tebl/C64-Kernal-Switcher/gallery/12f629 #1.PNG

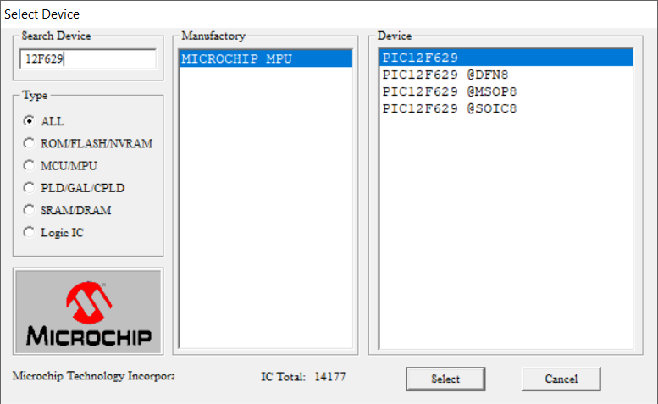
gallery/12f629 #1.PNG
