tebl/C64-Kernal-Switcher/gallery/12f629 #3.PNG

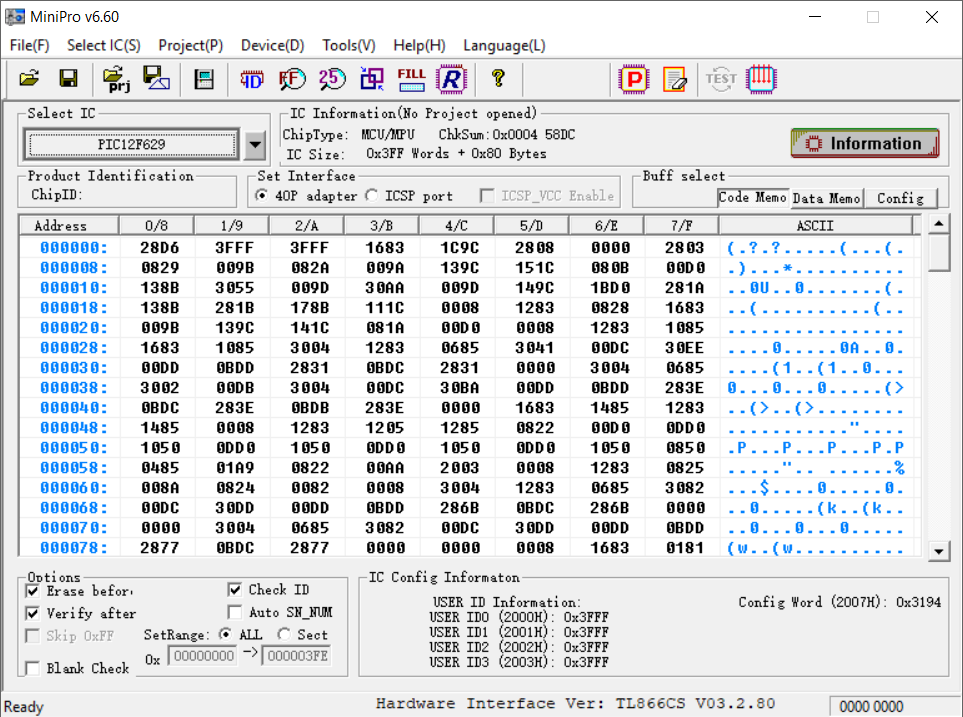
gallery/12f629 #3.PNG
