tebl/C64-Kernal-Switcher/gallery/27c256 #3.PNG

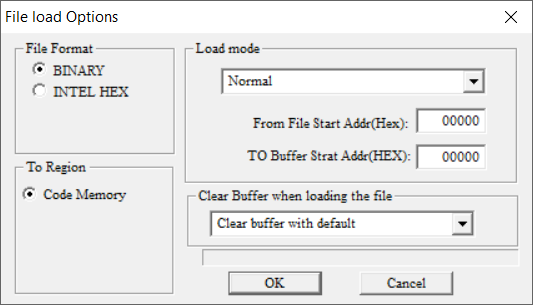
gallery/27c256 #3.PNG
