tebl/C64-Kernal-Switcher/gallery/27c256 #5.PNG

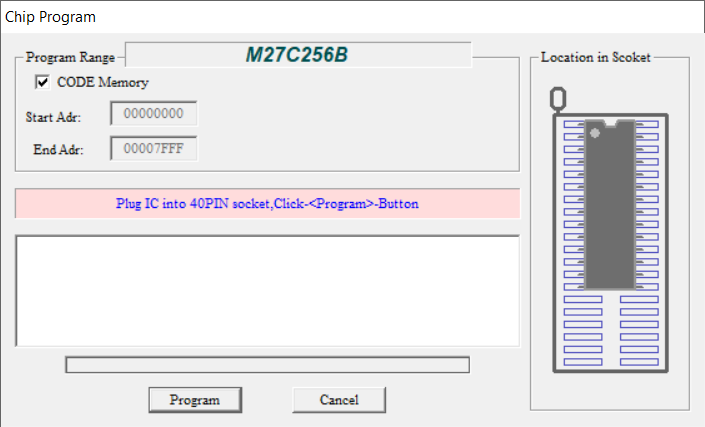
gallery/27c256 #5.PNG
