tebl/C64-Kernal-Switcher/gallery/Build #1.jpg

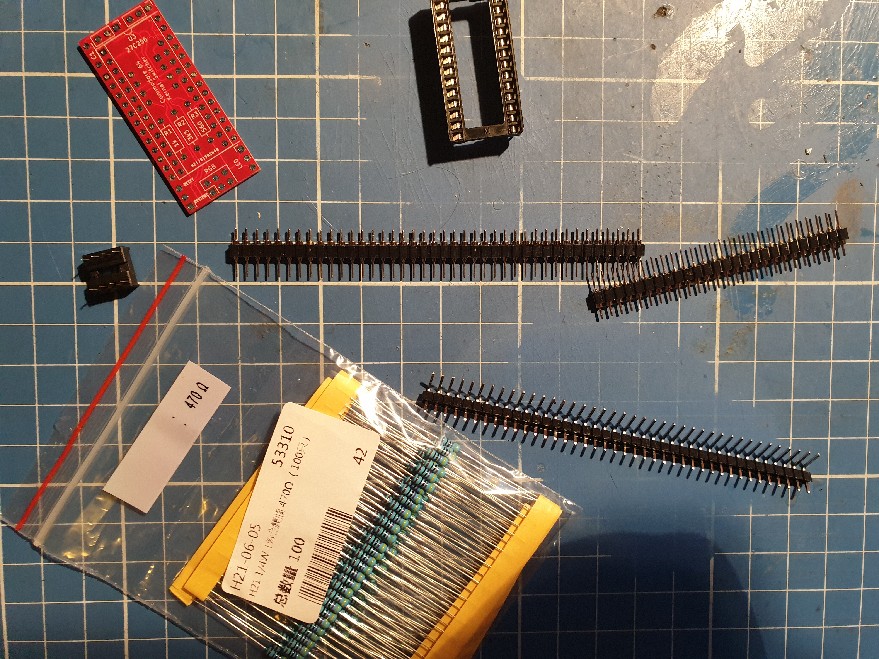
gallery/Build #1.jpg
