tebl/C64-Kernal-Switcher/gallery/Build #2.jpg

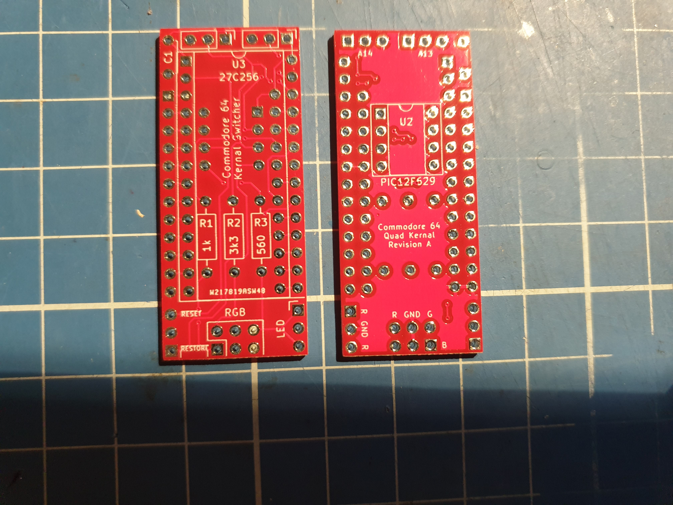
gallery/Build #2.jpg
